ChewbaccaBox/Demon-QB3-Sound-Board-Repro/Images/silkscreen.png

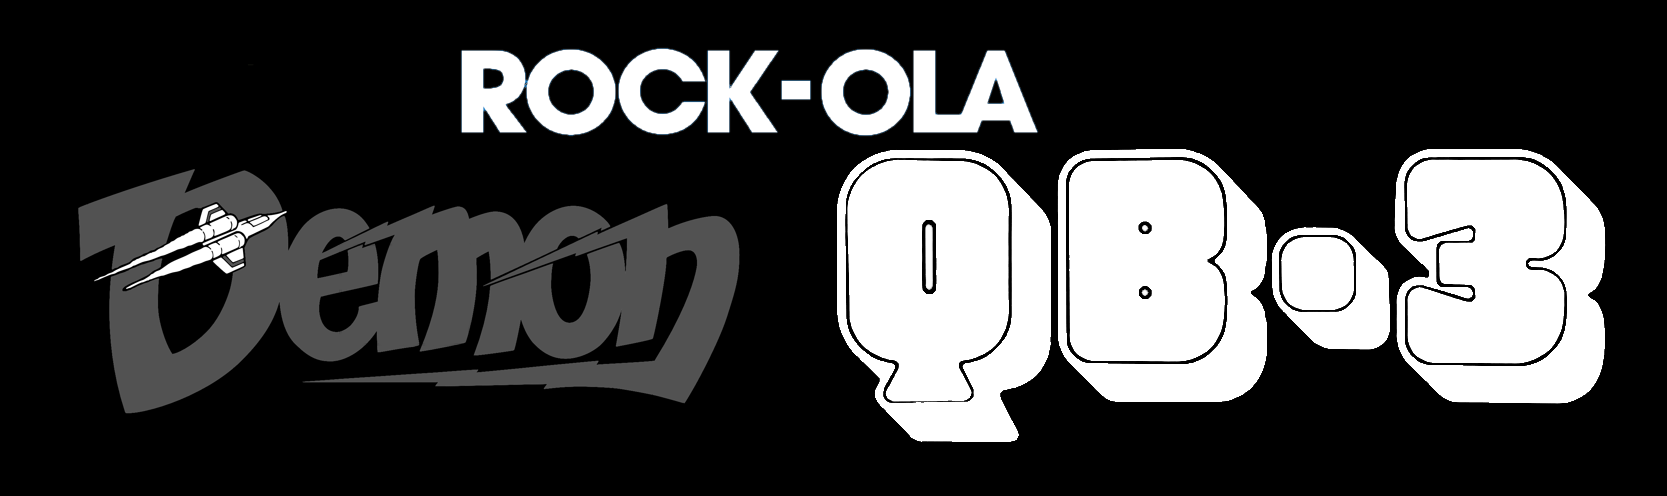
Images/silkscreen.png
